woodepic/Desk-Control/PCB/Working Prototype/IMG_3210.jpg

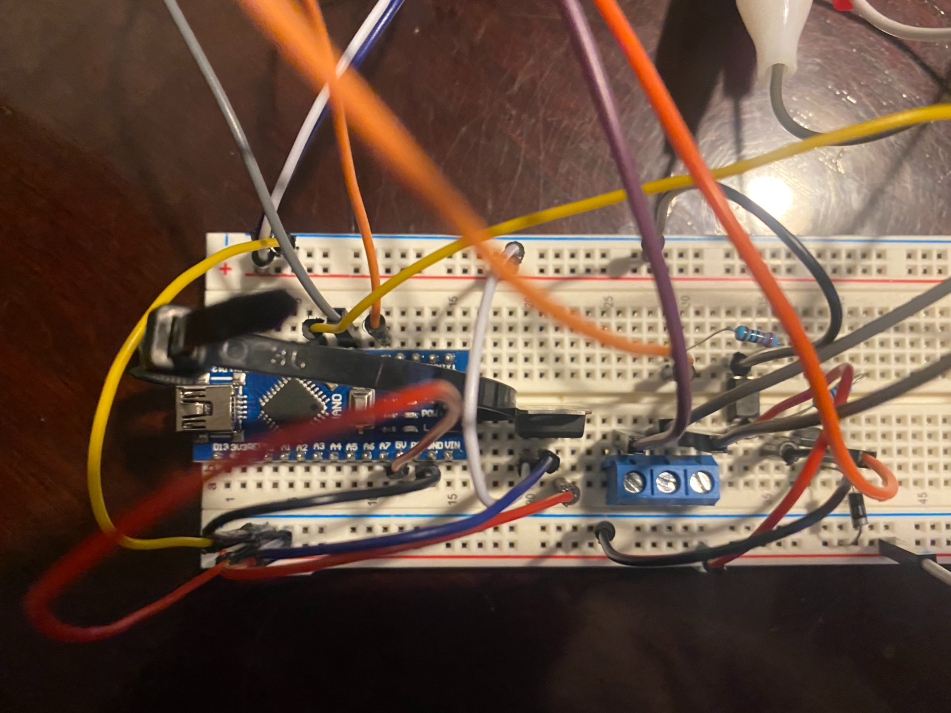
PCB/Working Prototype/IMG_3210.jpg
