woodepic/Desk-Control/PCB/Working Prototype/IMG_3532.jpg

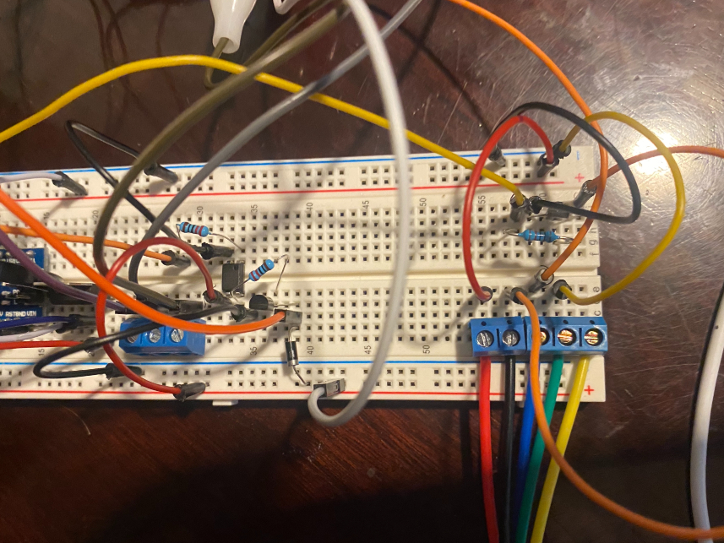
PCB/Working Prototype/IMG_3532.jpg
