woodepic/Desk-Control/PCB/Working Prototype/IMG_7579.jpg

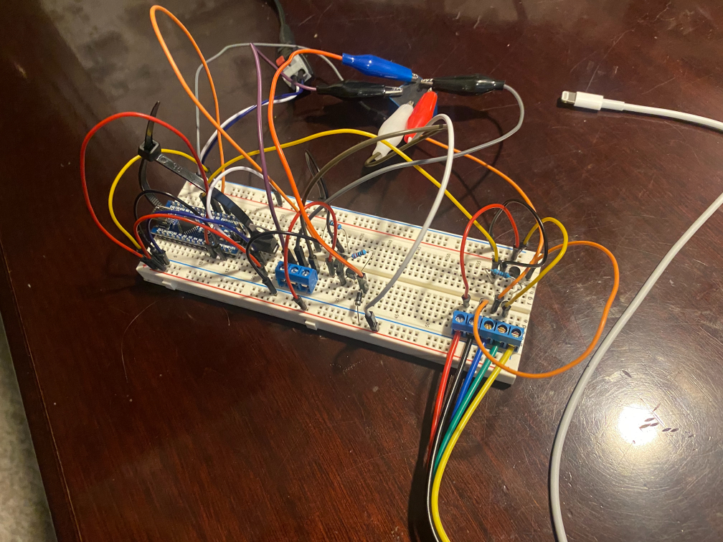
PCB/Working Prototype/IMG_7579.jpg
