woodepic/Desk-Control/PCB/Working Prototype/IMG_7609.jpg

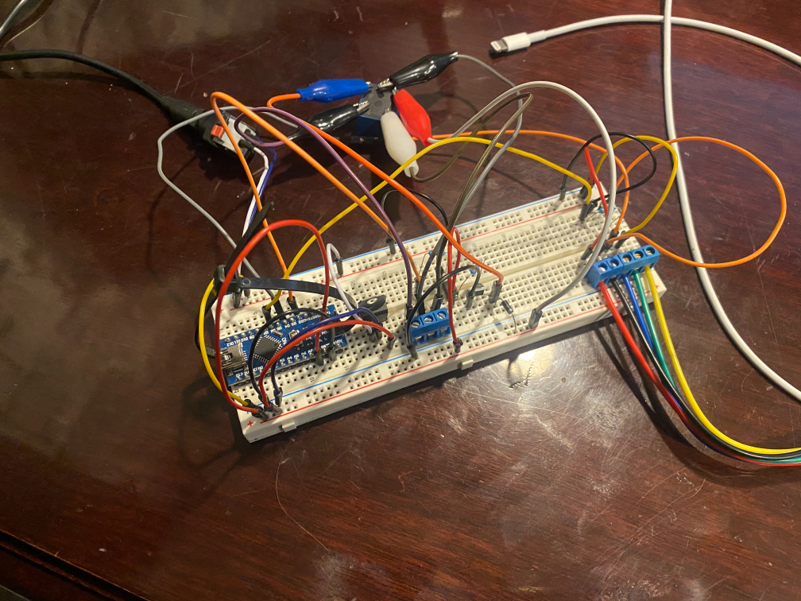
PCB/Working Prototype/IMG_7609.jpg
