woodepic/Desk-Control/PCB/Working Prototype/IMG_8094.jpg

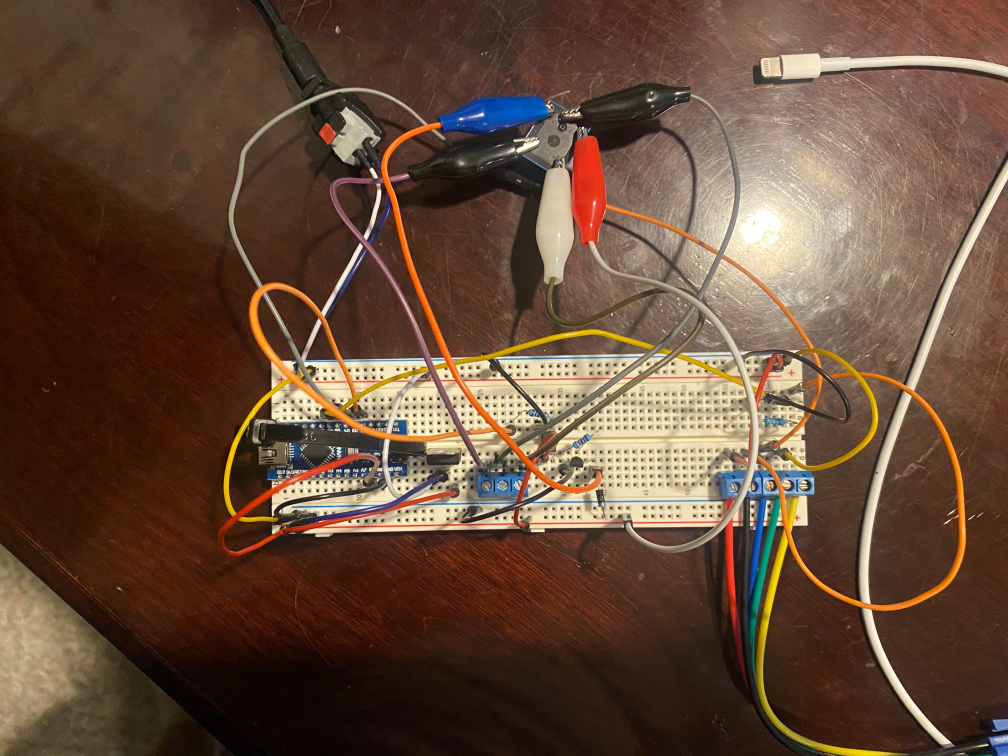
PCB/Working Prototype/IMG_8094.jpg
